mhardeman/matt-poe-prototype/visuals/switching-20260612-1.png

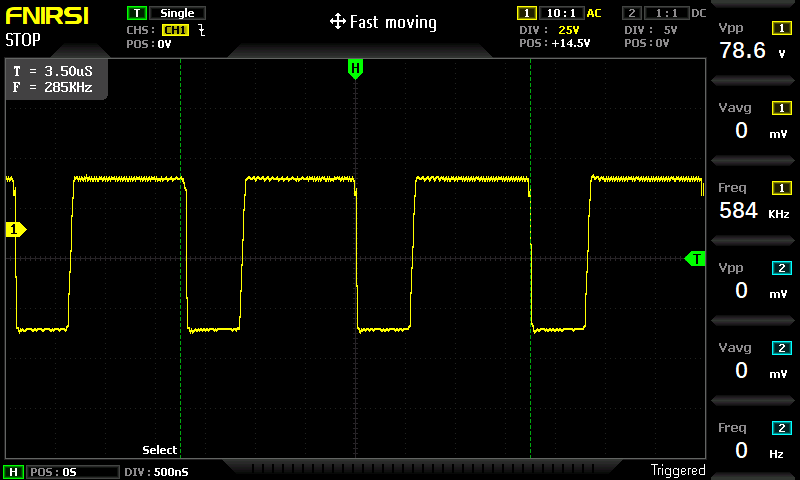
visuals/switching-20260612-1.png
